calphool/JMR-800/JX8P.h

const char* jx8p_param_names[256] = {
  // 0x00–0x7F: undefined, fill with ""
  "", // 0x00
  "", // 0x01
  "", // 0x02
  "", // 0x03
  "", // 0x04
  "", // 0x05
  "", // 0x06
  "", // 0x07
  "", // 0x08
  "", // 0x09
  "", // 0x0A
  "", // 0x0B
  "", // 0x0C
  "", // 0x0D
  "", // 0x0E
  "", // 0x0F
  "", // 0x10
  "", // 0x11
  "", // 0x12
  "", // 0x13
  "", // 0x14
  "", // 0x15
  "", // 0x16
  "", // 0x17
  "", // 0x18
  "", // 0x19
  "", // 0x1A
  "", // 0x1B
  "", // 0x1C
  "", // 0x1D
  "", // 0x1E
  "", // 0x1F
  "", // 0x20
  "", // 0x21
  "", // 0x22
  "", // 0x23
  "", // 0x24
  "", // 0x25
  "", // 0x26
  "", // 0x27
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

  // 0x80–0xAF: defined parameters
  "11 DCO1 Range    ",    // 0x80   -   0
  "12 DCO1 Waveform ",    // 0x81   -   1 
  "13 DCO1 Tune     ",    // 0x82   -   2
  "14 DCO1 LFO Depth",    // 0x83   -   3
  "15 DCO1 Env Depth",    // 0x84   -   4
  "21 DCO2 Range    ",    // 0x85   -   5
  "22 DCO2 Waveform ",    // 0x86   -   6
  "31 DCO XMOD      ",    // 0x87   -   7
  "23 DCO2 Tune     ",    // 0x88   -   8
  "32 DCO2 Fine Tune",    // 0x89   -   9
  "24 DCO2 LFO Depth",    // 0x8A   -  10
  "25 DCO2 Env Depth",    // 0x8B   -  11
  "",                     // 0x8C
  "",                     // 0x8D
  "",                     // 0x8E
  "33 DCO Dynamics  ",    // 0x8F   -  12
  "34 DCO EG Mode   ",    // 0x90   -  13
  "41 Mix DCO1      ",    // 0x91   -  14
  "42 Mix DCO2      ",    // 0x92   -  15
  "43 Mix Env       ",    // 0x93   -  16
  "44 Mix Dynamics  ",    // 0x94   -  17
  "45 Mix EG Mode   ",    // 0x95   -  18
  "51 VCF HPF       ",    // 0x96   -  19
  "52 VCF Freq      ",    // 0x97   -  20
  "53 VCF Resonance ",    // 0x98   -  21
  "54 VCF LFO       ",    // 0x99   -  22
  "55 VCF Env       ",    // 0x9A   -  23
  "56 VCF Key       ",    // 0x9B   -  24
  "57 VCF Dynamics  ",    // 0x9C   -  25
  "58 VCF EG Mode   ",    // 0x9D   -  26
  "61 VCA Level     ",    // 0x9E   -  27
  "63 VCA Dynamics  ",    // 0x9F   -  28
  "64 Chorus        ",    // 0xA0   -  29
  "71 LFO Waveform  ",    // 0xA1   -  30
  "72 LFO Delay     ",    // 0xA2   -  31
  "73 LFO Rate      ",    // 0xA3   -  32
  "81 EG Env1 Attk  ",    // 0xA4   -  33
  "82 EG Env1 Decay ",    // 0xA5   -  34
  "83 EG Env1 Sust  ",    // 0xA6   -  35
  "84 EG Env1 Rel   ",    // 0xA7   -  36
  "85 EG Env1 Key   ",    // 0xA8   -  37
  "91 EG Env2 Attk  ",    // 0xA9   -  38
  "92 EG Env2 Decay ",    // 0xAA   -  39
  "93 EG Env2 Sust  ",    // 0xAB   -  40
  "94 EG Env2 Rel   ",    // 0xAC   -  41
  "95 EG Env2 Key   ",    // 0xAD   -  42
  "",                     // 0xAE
  "62 VCA EG Mode   ",    // 0xAF   -  43
  "16 PMW1 Width    ",    // 0xB0   -  44
  "17 PWM1 Env      ",    // 0xB1   -  45
  "18 PMW1 LFO      ",    // 0xB2   -  46
  "26 PWM2 Width    ",    // 0xB3   -  47
  "28 PWM2 Env      ",    // 0xB4   -  48
  "27 PWM2 LFO      ",    // 0xB5   -  49
  "", // 0xB6
  "", // 0xB7
  "", // 0xB8
  "", // 0xB9
  "", // 0xBA
  "", // 0xBB
  "", // 0xBC
  "", // 0xBD
  "", // 0xBE
  "", // 0xBF
  "", // 0xC0
  "", // 0xC1
  "", // 0xC2
  "", // 0xC3
  "", // 0xC4
  "", // 0xC5
  "", // 0xC6
  "", // 0xC7
  "", // 0xC8
  "", // 0xC9
  "", // 0xCA
  "", // 0xCB
  "", // 0xCC
  "", // 0xCD
  "35 PWM Dyna      ",       // 0xCE   -  50
  "", // 0xCF
  "74 LFO Sync      ",       // 0xD0   -  51
  "", // 0xD1
  "", // 0xD2
  "", // 0xD3
  "", // 0xD4
  "", // 0xD5
  "36 PWM Mode      ",       // 0xD6   -  52
  "", // 0xD7
  "", // 0xD8
  "", // 0xD9
  "", // 0xDA
  "", // 0xDB
  "", // 0xDC
  "", // 0xDD
  "", // 0xDE
  "", // 0xDF
  "", // 0xE0
  "ROM TONE?        ",         // 0xE1  - Write command maybe?   - 53
  "", // 0xE2
  "", // 0xE3
  "", // 0xE4
  "", // 0xE5
  "", // 0xE6
  "", // 0xE7
  "", // 0xE8
  "", // 0xE9
  "", // 0xEA
  "", // 0xEB
  "", // 0xEC
  "", // 0xED
  "", // 0xEE
  "", // 0xEF
  "", // 0xF0
  "", // 0xF1
  "", // 0xF2
  "", // 0xF3
  "", // 0xF4
  "", // 0xF5
  "", // 0xF6
  "", // 0xF7
  "", // 0xF8
  "", // 0xF9
  "", // 0xFA
  "", // 0xFB
  "", // 0xFC
  "", // 0xFD
  "", // 0xFE
  ""  // 0xFF
};


#define PARAM_TYPES_COUNT 11
#define NUMERIC_PARAM 0
#define FOUR_VALUE_PARAM 1
#define WAVE_PARAM 2
#define RANGE_PARAM 3
#define XMOD_PARAM 4
#define EG_MODE_PARAM 5
#define TUNE_PARAM 6
#define FINE_PARAM 7
#define VCA_EG_MODE 8
#define LFO_WAVE 9
#define CHORUS 10


#define NUM_PARAMS 52
uint8_t paramIndexTable[NUM_PARAMS] = {
 0x80, 0x81, 0x82, 0x83, 0x84, 0x85, 0x86, 0x87, 0x88, 0x89, 0x8a, 0x8b,
 0x8F, 0x90, 0x91, 0x92, 0x93, 0x94, 0x95, 0x96, 0x97, 0x98, 0x99, 0x9b,
 0x9c, 0x9d, 0x9e, 0x9f, 0xa0, 0xa1, 0xa2, 0xa3, 0xa4, 0xa5, 0xa6, 0xa7,
 0xa8, 0xa9, 0xaa, 0xab, 0xac, 0xad, 0xaf, 0xb0, 0xb1, 0xb2, 0xb3, 0xb4, 
 0xb5, 0xce, 0xd0, 0xd6
};

uint8_t activeParams[NUM_PARAMS] = {
 0x01, 0x01, 0x00, 0x00, 0x00, 0x00, 0x00, 0x00, 0x00, 0x00, 0x00, 0x00,
 0x00, 0x00, 0x00, 0x00, 0x00, 0x00, 0x00, 0x00, 0x00, 0x00, 0x00, 0x00,
 0x00, 0x00, 0x00, 0x00, 0x00, 0x00, 0x00, 0x00, 0x00, 0x00, 0x00, 0x00,
 0x00, 0x00, 0x00, 0x00, 0x00, 0x00, 0x00, 0x00, 0x00, 0x00, 0x00, 0x00, 
 0x00, 0x00, 0x00, 0x00 
};


const int8_t arrow_dx[360] = {
  -1, -2, -2, -2, -2, -2, -2, -2, -2, -2, -2, -2,
  -2, -2, -2, -2, -2, -2, -2, -2, -2, -2, -2, -2,
  -2, -2, -2, -3, -3, -3, -3, -3, -3, -3, -3, -3,
  -3, -3, -3, -3, -3, -3, -3, -3, -3, -3, -3, -3,
  -3, -3, -3, -3, -3, -3, -3, -3, -3, -3, -3, -3,
  -3, -3, -3, -3, -3, -3, -3, -3, -3, -3, -3, -3,
  -3, -3, -3, -3, -3, -3, -3, -3, -3, -3, -3, -3,
  -3, -3, -3, -3, -3, -3, -3, -3, -3, -3, -2, -2,
  -2, -2, -2, -2, -2, -2, -2, -2, -2, -2, -2, -2,
  -2, -2, -2, -2, -2, -2, -2, -2, -2, -2, -2, -2,
  -2, -1, -1, -1, -1, -1, -1, -1, -1, -1, -1, -1,
  -1, -1, -1, -1, -1, -1, -1, -1, -1,  0,  0,  0,
   0,  0,  0,  0,  0,  0,  0,  0,  0,  0,  0,  0,
   0,  0,  0,  0,  1,  1,  1,  1,  1,  1,  1,  1,
   1,  1,  1,  1,  1,  1,  1,  1,  1,  1,  1,  1,
   2,  2,  2,  2,  2,  2,  2,  2,  2,  2,  2,  2,
   2,  2,  2,  2,  2,  2,  2,  2,  2,  2,  2,  2,
   2,  2,  2,  3,  3,  3,  3,  3,  3,  3,  3,  3,
   3,  3,  3,  3,  3,  3,  3,  3,  3,  3,  3,  3,
   3,  3,  3,  3,  3,  3,  3,  3,  3,  3,  3,  3,
   3,  3,  3,  3,  3,  3,  3,  3,  3,  3,  3,  3,
   3,  3,  3,  3,  3,  3,  3,  3,  3,  3,  3,  3,
   3,  3,  3,  3,  3,  3,  3,  3,  3,  3,  2,  2,
   2,  2,  2,  2,  2,  2,  2,  2,  2,  2,  2,  2,
   2,  2,  2,  2,  2,  2,  2,  2,  2,  2,  2,  2,
   2,  1,  1,  1,  1,  1,  1,  1,  1,  1,  1,  1,
   1,  1,  1,  1,  1,  1,  1,  1,  1,  0,  0,  0,
   0,  0,  0,  0,  0,  0,  0,  0,  0,  0,  0,  0,
   0,  0,  0,  0, -1, -1, -1, -1, -1, -1, -1, -1,
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
   3,  3,  3,  3,  3,  3,  3,  3,  3,  3,  3,  3,
   3,  3,  3,  3,  3,  3,  3,  3,  3,  3,  3,  3,
   3,  3,  3,  3,  3,  3,  3,  3,  3,  3,  3,  3,
   3,  3,  3,  3,  3,  3,  3,  3,  3,  3,  3,  3,
   3,  3,  3,  3,  3,  3,  3,  3,  3,  3,  3,  3,
};
